BentoOre0/2025-2026-UBC-ROCKET-work/star-raptor/media/cad/cad-wireframe-angled.jpg

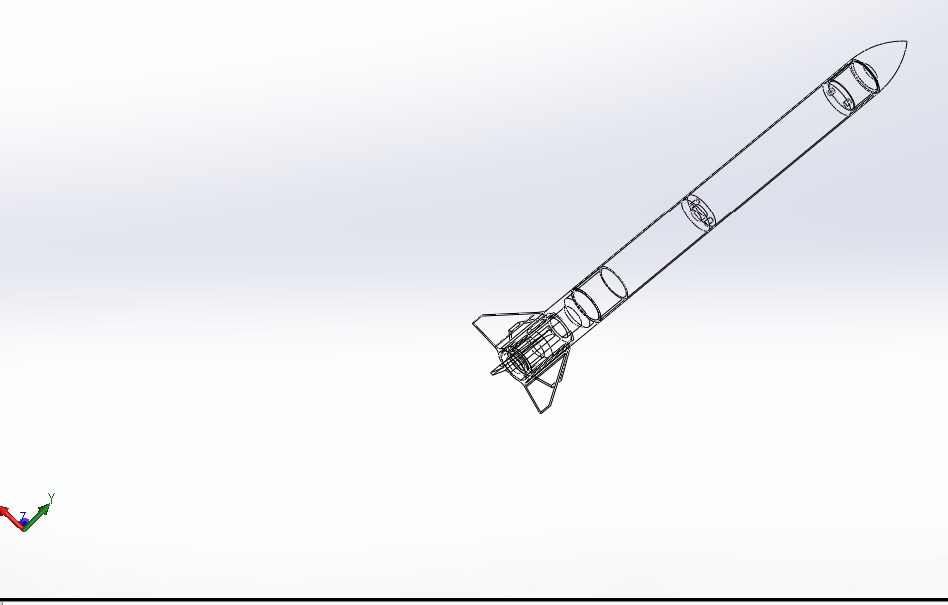
star-raptor/media/cad/cad-wireframe-angled.jpg
