BentoOre0/2025-2026-UBC-ROCKET-work/star-raptor/media/cad/cad-wireframe-full.jpg

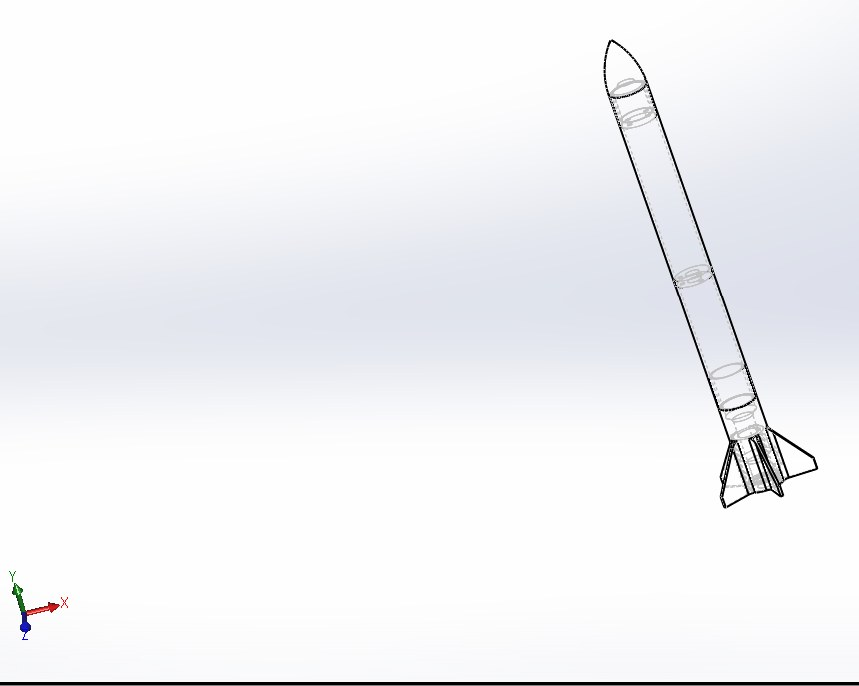
star-raptor/media/cad/cad-wireframe-full.jpg
